EliaKr/ESP32CAM-Weather-Station/electronics/ESP32CAM-Weather-Station/ESP32CAM-Weather-Station.kicad_sch

## KiCad design electronics/ESP32CAM-Weather-Station/ESP32CAM-Weather-Station.kicad_sch (2026-02-18)

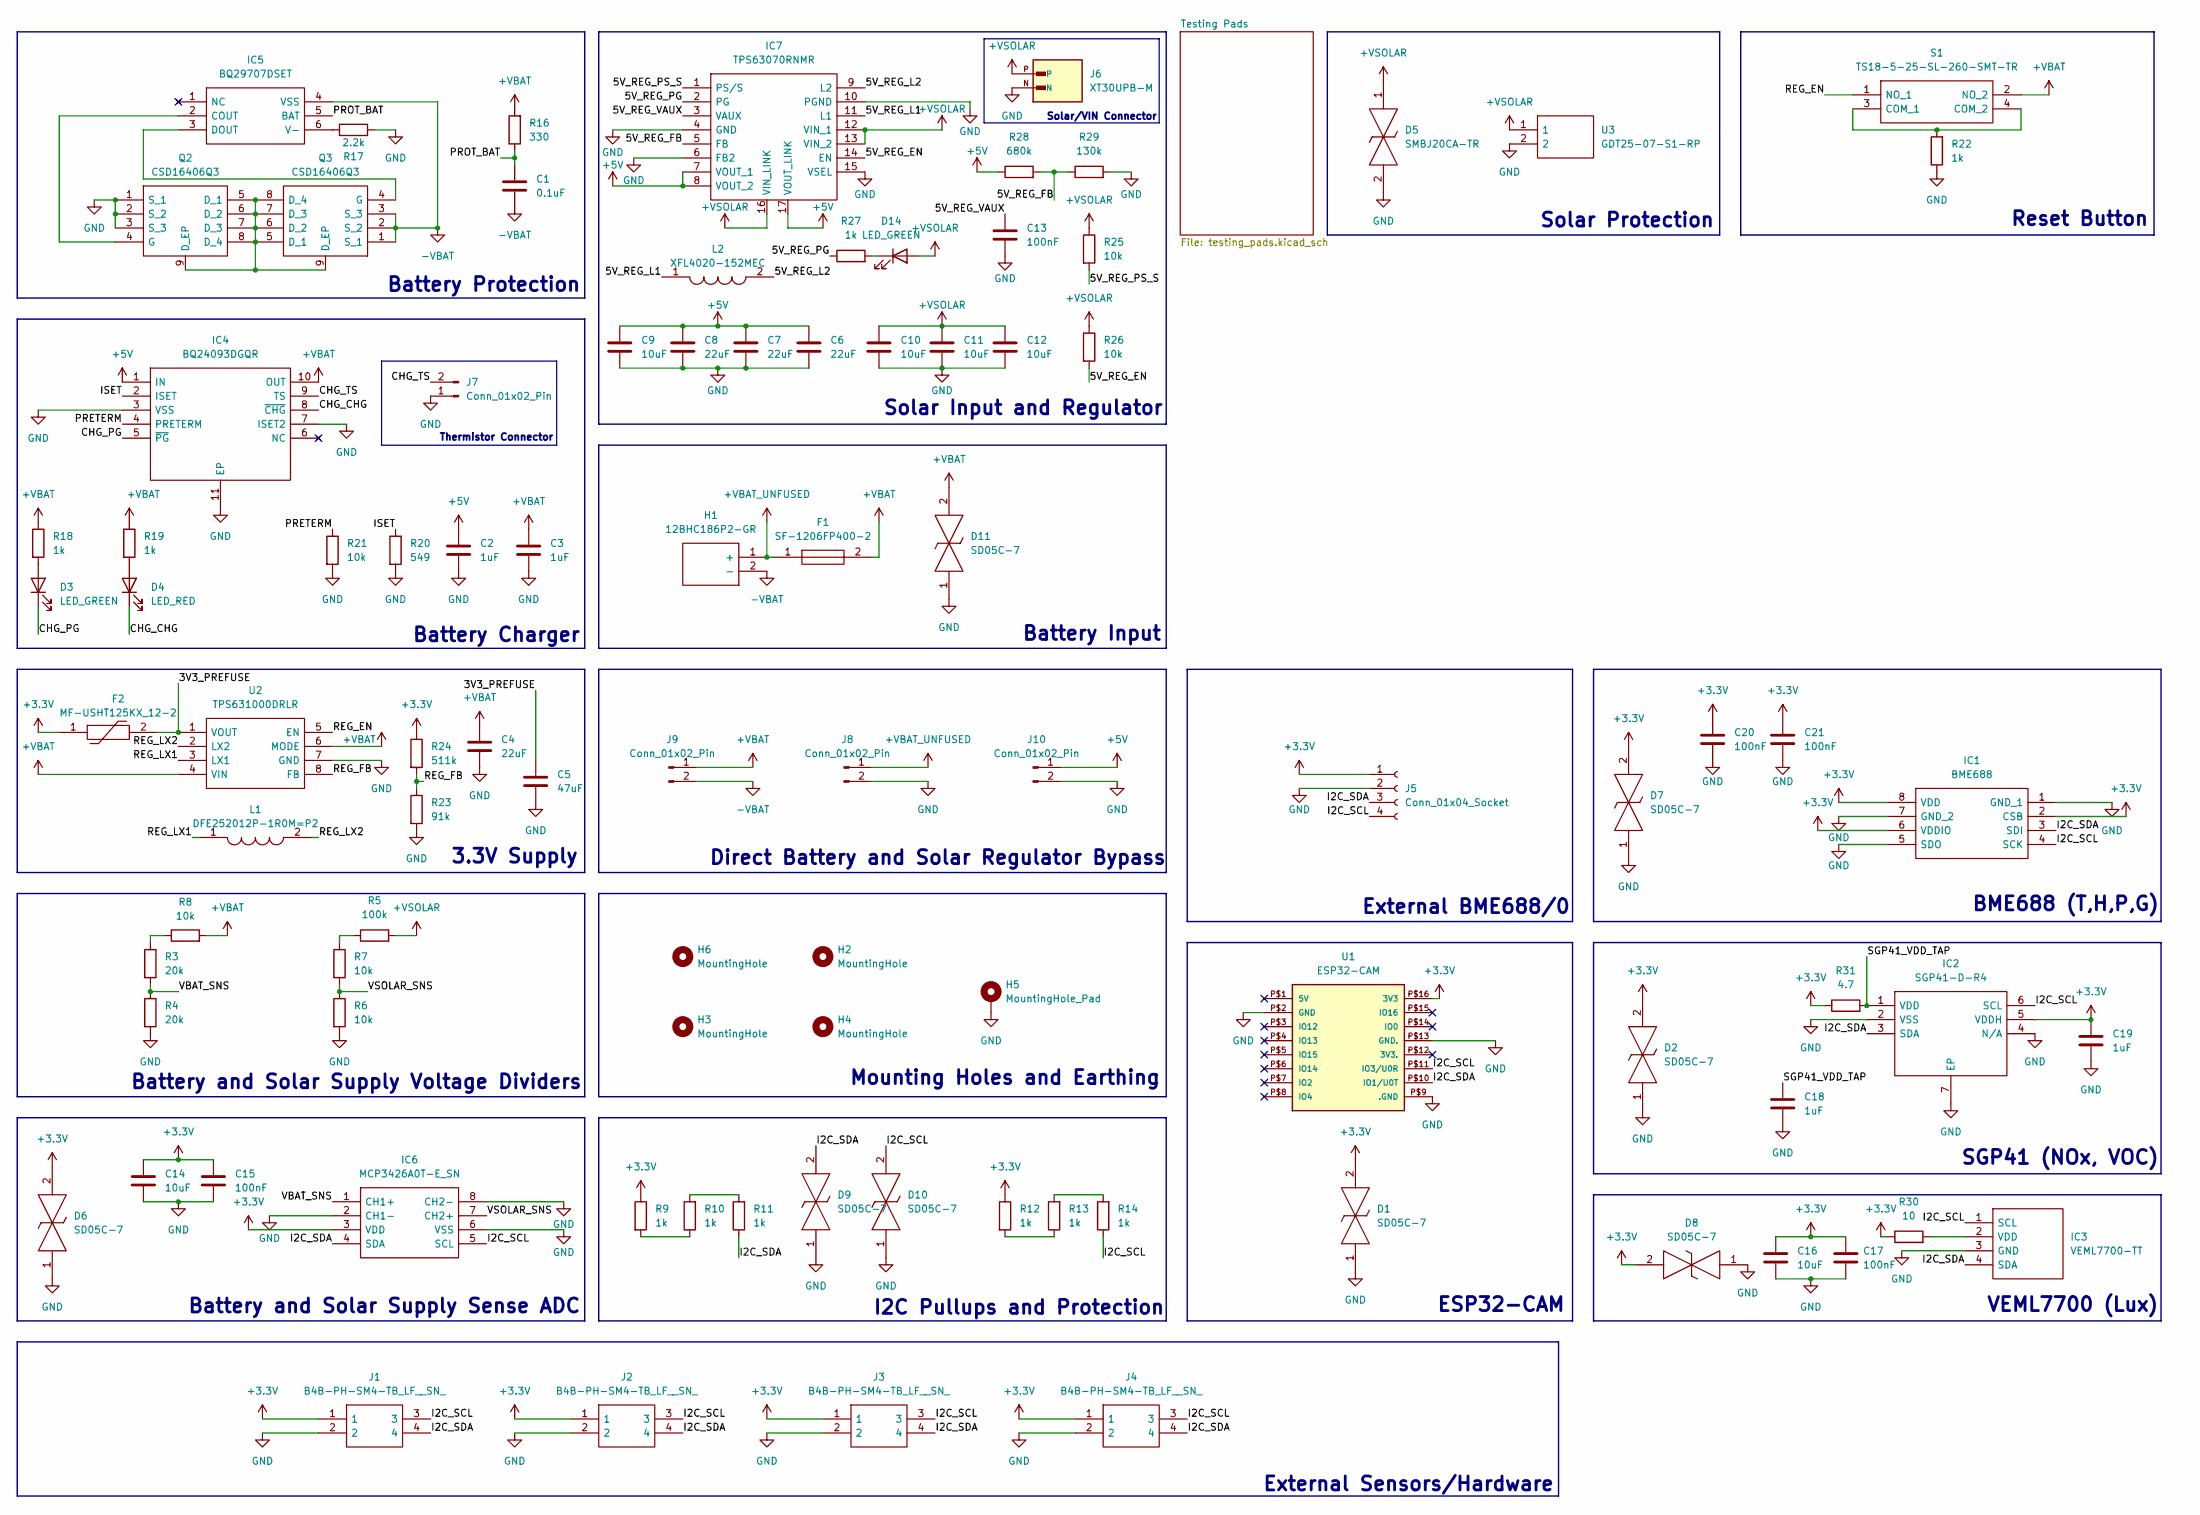
[picture p13: schematic ESP32CAM-Weather-Station.kicad_sch]

Parts:
C1: 0.1uF; C_0805_2012Metric_Pad1.18x1.45mm_HandSolder
C2, C3, C18, C19: 1uF; C_0805_2012Metric_Pad1.18x1.45mm_HandSolder
C4: 22uF; C_0603_1608Metric_Pad1.08x0.95mm_HandSolder
C5: 47uF; C_0805_2012Metric_Pad1.18x1.45mm_HandSolder
C6, C7, C8: 22uF; C_0805_2012Metric_Pad1.18x1.45mm_HandSolder
C9, C10: 10uF; C_0603_1608Metric_Pad1.08x0.95mm_HandSolder
C11, C12, C14, C16: 10uF; C_0805_2012Metric_Pad1.18x1.45mm_HandSolder
C13, C15, C17, C20, C21: 100nF; C_0603_1608Metric_Pad1.08x0.95mm_HandSolder
D1, D2, D6, D7, D8, D9, D10, D11: SD05C-7; SOD2513X120N; Mouser Part Number 621-SD05C-7
D3, D14: LED_GREEN; LED_0805_2012Metric_Pad1.15x1.40mm_HandSolder
D4: LED_RED; LED_0805_2012Metric_Pad1.15x1.40mm_HandSolder
D5: SMBJ20CA-TR; DIONM5436X265N; Mouser Part Number 511-SMBJ20CA
F1: SF-1206FP400-2; FUSC3116X70N; Mouser Part Number 652-SF-1206FP400-2
F2: MF-USHT125KX_12-2; MFUSHT125KX122; Mouser Part Number 652-MF-USHT125KX/12
H1: 12BHC186P2-GR; 12BHC186P2GR; Mouser Part Number 12BHC186P2-GR
H2, H3, H4, H6: MountingHole; MountingHole_3.2mm_M3_Pad_Via
H5: MountingHole_Pad; MountingHole_3.2mm_M3_DIN965_Pad
IC1: BME688; Mouser Part Number 262-BME688
IC2: SGP41-D-R4; SON80P244X244X95-7N; Mouser Part Number 403-SGP41-D-R4
IC3: VEML7700-TT; VEML7700; Mouser Part Number 78-VEML7700-TT
IC4: BQ24093DGQR; SOP50P490X110-11N; Mouser Part Number 595-BQ24093DGQR
IC5: BQ29707DSET; TPS610985DSET; Mouser Part Number 595-BQ29707DSET
IC6: MCP3426A0T-E_SN; SOIC127P600X175-8N; Mouser Part Number 579-MCP3426A0TE/SN
IC7: TPS63070RNMR; TPS630701RNMR; Mouser Part Number 595-TPS63070RNMR
J1, J2, J3, J4: B4B-PH-SM4-TB_LF__SN_; B4B-PH-SM4_1; Mouser Part Number N/A
J5: Conn_01x04_Socket; PinHeader_1x04_P2.54mm_Vertical
J6: XT30UPB-M; AMASS_XT30UPB-M
J7, J8, J9, J10: Conn_01x02_Pin; PinHeader_1x02_P2.54mm_Vertical
L1: DFE252012P-1R0M=P2; DFE2HCAH1R0MJ0L; Mouser Part Number 81-DFE252012P-1R0MP2
L2: XFL4020-152MEC; XFL4020152MEC; Mouser Part Number 994-XFL4020-152MEC
Q2, Q3: CSD16406Q3; DQG_VSON-CLIP; Mouser Part Number 595-CSD16406Q3
R3, R4: 20k; R_0805_2012Metric_Pad1.20x1.40mm_HandSolder
R5: 100k; R_0805_2012Metric_Pad1.20x1.40mm_HandSolder
R6, R7, R8, R21, R25, R26: 10k; R_0805_2012Metric_Pad1.20x1.40mm_HandSolder
R9, R10, R11, R12, R13, R14, R18, R19, R22, R27: 1k; R_0805_2012Metric_Pad1.20x1.40mm_HandSolder
R16: 330; R_0805_2012Metric_Pad1.20x1.40mm_HandSolder
R17: 2.2k; R_0805_2012Metric_Pad1.20x1.40mm_HandSolder
R20: 549; R_0805_2012Metric_Pad1.20x1.40mm_HandSolder
R23: 91k; R_0805_2012Metric_Pad1.20x1.40mm_HandSolder
R24: 511k; R_0805_2012Metric_Pad1.20x1.40mm_HandSolder
R28: 680k; R_0805_2012Metric_Pad1.20x1.40mm_HandSolder
R29: 130k; R_0805_2012Metric_Pad1.20x1.40mm_HandSolder
R30: 10; R_0805_2012Metric_Pad1.20x1.40mm_HandSolder
R31: 4.7; R_0805_2012Metric_Pad1.20x1.40mm_HandSolder
S1: TS18-5-25-SL-260-SMT-TR; TS18525SL260SMTTR; Mouser Part Number 179-TS18525SL260SMTT
U1: ESP32-CAM
U2: TPS631000DRLR; SOTFL50P160X60-8N; Mouser Part Number 595-TPS631000DRLR
U3: GDT25-07-S1-RP; GDT2507S1RP; Mouser Part Number 652-GDT25-07-S1-RP

Connections:
3V3_PREFUSE: C5.1, F2.2, U2.1 (VOUT)
5V_REG_EN: IC7.14 (EN), R26.2
5V_REG_FB: IC7.5 (FB), R28.2, R29.1
5V_REG_L1: IC7.11 (L1), L2.1
5V_REG_L2: IC7.9 (L2), L2.2
5V_REG_PG: IC7.2 (PG), R27.1
5V_REG_PS_S: IC7.1 (PS/S), R25.2
5V_REG_VAUX: C13.2, IC7.3 (VAUX)
+3.3V: C14.1, C15.2, C16.1, C17.2, C19.1, C20.2, C21.2, D1.2, D2.2, D6.2, D7.2, D8.2, F2.1, IC1.2 (CSB), IC1.6 (VDDIO), IC1.8 (VDD), IC2.5 (VDDH), IC6.3 (VDD), J1.1, J2.1, J3.1, J4.1, J5.1, R9.1, R12.1, R24.1, R30.1, R31.1, U1.P$16 (3V3)
+5V: C2.1, C6.1, C7.1, C8.1, C9.1, IC4.1 (IN), IC7.7 (VOUT_1), IC7.8 (VOUT_2), IC7.17 (VOUT_LINK), J10.1, R28.1
+VBAT: C3.1, C4.1, D11.2, F1.2, IC4.10 (OUT), J9.1, R8.2, R16.2, R18.1, R19.1, S1.2 (NO_2), U2.4 (VIN), U2.6 (MODE)
+VBAT_UNFUSED: F1.1, H1.1 (+), J8.1
+VSOLAR: C10.1, C11.1, C12.1, D5.1, D14.2 (A), IC7.12 (VIN_1), IC7.13 (VIN_2), IC7.16 (VIN_LINK), J6.P, R5.2, R25.1, R26.1, U3.1
-VBAT: C1.2, H1.2 (-), IC5.4 (VSS), J9.2, Q3.1 (S_1), Q3.2 (S_2), Q3.3 (S_3)
CHG_CHG: D4.1 (K), IC4.8 (~CHG)
CHG_PG: D3.1 (K), IC4.5 (~PG)
CHG_TS: IC4.9 (TS), J7.2
GND: C2.2, C3.2, C4.2, C5.2, C6.2, C7.2, C8.2, C9.2, C10.2, C11.2, C12.2, C13.1, C14.2, C15.1, C16.2, C17.1, C18.2, C19.2, C20.1, C21.1, D1.1, D2.1, D5.2, D6.1, D7.1, D8.1, D9.1, D10.1, D11.1, H5.1, IC1.1 (GND_1), IC1.5 (SDO), IC1.7 (GND_2), IC2.2 (VSS), IC2.4 (N/A), IC2.7 (EP), IC3.3 (GND), IC4.3 (VSS), IC4.7 (ISET2), IC4.11 (EP), IC6.2 (CH1-), IC6.6 (VSS), IC6.8 (CH2-), IC7.4 (GND), IC7.6 (FB2), IC7.10 (PGND), IC7.15 (VSEL), J1.2, J2.2, J3.2, J4.2, J5.2, J6.N, J7.1, J8.2, J10.2, Q2.1 (S_1), Q2.2 (S_2), Q2.3 (S_3), R4.2, R6.2, R17.1, R20.2, R21.2, R22.1, R23.2, R29.2, U1.P$2 (GND), U1.P$9 (.GND), U1.P$13 (GND.), U2.7 (GND), U3.2
I2C_SCL: D10.2, IC1.4 (SCK), IC2.6 (SCL), IC3.1 (SCL), IC6.5 (SCL), J1.3, J2.3, J3.3, J4.3, J5.4, R14.1, U1.P$11 (IO3/U0R)
I2C_SDA: D9.2, IC1.3 (SDI), IC2.3 (SDA), IC3.4 (SDA), IC6.4 (SDA), J1.4, J2.4, J3.4, J4.4, J5.3, R11.1, U1.P$10 (IO1/U0T)
ISET: IC4.2 (ISET), R20.1
unnamed: D3.2 (A), R18.2
unnamed: D4.2 (A), R19.2
unnamed: D14.1 (K), R27.2
unnamed: IC3.2 (VDD), R30.2
unnamed: IC5.2 (COUT), Q2.4 (G)
unnamed: IC5.3 (DOUT), Q3.4 (G)
unnamed: IC5.6 (V-), R17.2
unnamed: Q2.5 (D_1), Q2.6 (D_2), Q2.7 (D_3), Q2.8 (D_4), Q2.9 (D_EP), Q3.5 (D_1), Q3.6 (D_2), Q3.7 (D_3), Q3.8 (D_4), Q3.9 (D_EP)
unnamed: R3.1, R8.1
unnamed: R5.1, R7.1
unnamed: R9.2, R10.1
unnamed: R10.2, R11.2
unnamed: R12.2, R13.1
unnamed: R13.2, R14.2
unnamed: R22.2, S1.3 (COM_1), S1.4 (COM_2)
PRETERM: IC4.4 (PRETERM), R21.1
PROT_BAT: C1.1, IC5.5 (BAT), R16.1
REG_EN: S1.1 (NO_1), U2.5 (EN)
REG_FB: R23.1, R24.2, U2.8 (FB)
REG_LX1: L1.1, U2.3 (LX1)
REG_LX2: L1.2, U2.2 (LX2)
SGP41_VDD_TAP: C18.1, IC2.1 (VDD), R31.2
VBAT_SNS: IC6.1 (CH1+), R3.2, R4.1
VSOLAR_SNS: IC6.7 (CH2+), R6.1, R7.2

Notes on the sheet:
SGP41 (NOx, VOC)
Mounting Holes and Earthing
Battery and Solar Supply Voltage Dividers
3.3V Supply
Battery and Solar Supply Sense ADC
Battery Charger
Battery Protection
Solar/VIN Connector
I2C Pullups and Protection
Battery Input
External Sensors/Hardware
ESP32-CAM
Direct Battery and Solar Regulator Bypass
Reset Button
Solar Input and Regulator
External BME688/0
Solar Protection
VEML7700 (Lux)
BME688 (T,H,P,G)
Thermistor Connector
